CMUAbstract/pq-cdh-su22/versions/pq-cdh-su22-qpi/versions/README.md

# Versions

ZIP files containing Gerbers for the most recent and past board versions

## Directory Contents

* [README.md](README.md): This document

## License

Written by Bradley Denby  
Other contributors: None

See the top-level [../LICENSE](LICENSE) file for the license.
