CMUAbstract/pq-cdh-su22/software/cdh_flight_Rx_Tx/support/support.h

// support.h
// Tartan Artibeus CDH UART header file
//
// Written by Bradley Denby
// Other contributors: None
//
// See the top-level LICENSE file for the license.

#ifndef SUPPORT_H
#define SUPPORT_H

// Initialization functions

void init_clock(void);
void init_led(void);
void init_uart(void);


#endif
